wahyukusumo/RP2040-Macropad/Kicad/RP2040-Macropad/RP2040-Macropad.kicad_sch

## KiCad design Kicad/RP2040-Macropad/RP2040-Macropad.kicad_sch (2025-09-22)

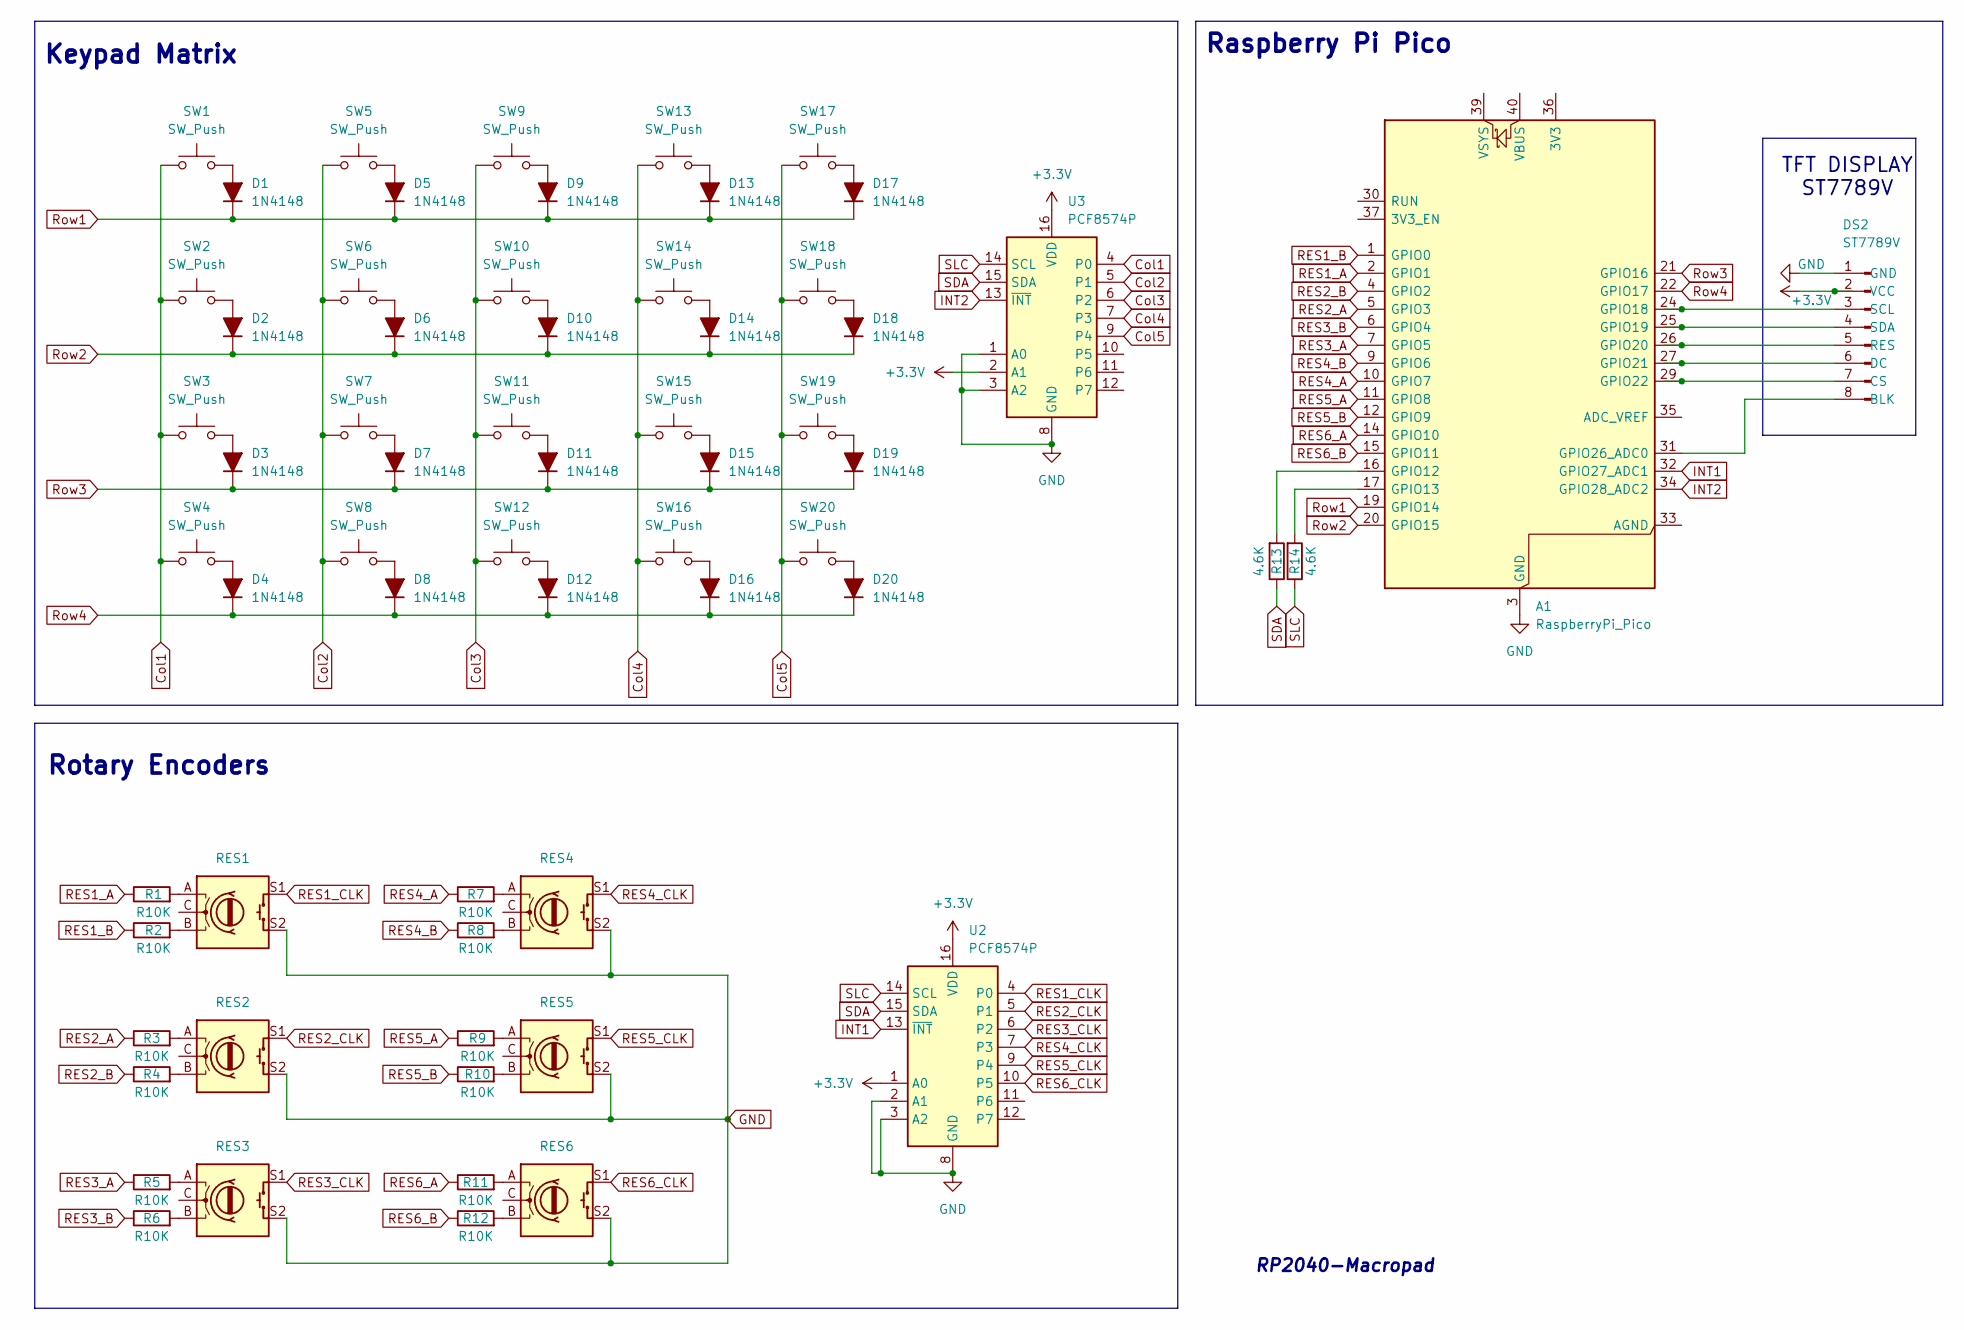
[picture p6: schematic RP2040-Macropad.kicad_sch]

Parts:
A1: RaspberryPi_Pico; RaspberryPi_Pico_Common_Unspecified
D1, D2, D3, D4, D5, D6, D7, D8, D9, D10, D11, D12, D13, D14, D15, D16, D17, D18, D19, D20: 1N4148; D_DO-35_SOD27_P7.62mm_Horizontal
DS2: ST7789V; PinHeader_1x07_P2.54mm_Vertical
R1, R2, R3, R4, R5, R6, R7, R8, R9, R10, R11, R12: R10K; R_0805_2012Metric_Pad1.20x1.40mm_HandSolder
R13, R14: 4.6K; R_Axial_DIN0204_L3.6mm_D1.6mm_P7.62mm_Horizontal
RES1_CLK1: RES1; RotaryEncoder_Alps_EC11E-Switch_Vertical_H20mm
RES2_CLK1: RES2; RotaryEncoder_Alps_EC11E-Switch_Vertical_H20mm
RES3_CLK1: RES3; RotaryEncoder_Alps_EC11E-Switch_Vertical_H20mm
RES4_CLK1: RES4; RotaryEncoder_Alps_EC11E-Switch_Vertical_H20mm
RES5_CLK1: RES5; RotaryEncoder_Alps_EC11E-Switch_Vertical_H20mm
RES6_CLK1: RES6; RotaryEncoder_Alps_EC11E-Switch_Vertical_H20mm
SW1, SW2, SW3, SW4, SW5, SW6, SW7, SW8, SW9, SW10, SW11, SW12, SW13, SW14, SW15, SW16, SW17, SW18, SW19, SW20: SW_Push; SW_Hotswap_Kailh_MX
U2, U3: PCF8574P; DIP-16_W7.62mm

Connections:
+3.3V: DS2.2 (VCC), U2.1 (A0), U2.16 (VDD), U3.2 (A1), U3.16 (VDD)
Col1: SW1.1, SW2.1, SW3.1, SW4.1, U3.4 (P0)
Col2: SW5.1, SW6.1, SW7.1, SW8.1, U3.5 (P1)
Col3: SW9.1, SW10.1, SW11.1, SW12.1, U3.6 (P2)
Col4: SW13.1, SW14.1, SW15.1, SW16.1, U3.7 (P3)
Col5: SW17.1, SW18.1, SW19.1, SW20.1, U3.9 (P4)
GND: A1.3 (GND), A1.8 (GND), A1.13 (GND), A1.18 (GND), A1.23 (GND), A1.28 (GND), A1.38 (GND), DS2.1 (GND), RES1_CLK1.S2, RES2_CLK1.S2, RES3_CLK1.S2, RES4_CLK1.S2, RES5_CLK1.S2, RES6_CLK1.S2, U2.2 (A1), U2.3 (A2), U2.8 (GND), U3.1 (A0), U3.3 (A2), U3.8 (GND)
INT1: A1.32 (GPIO27_ADC1), U2.13 (~INT)
INT2: A1.34 (GPIO28_ADC2), U3.13 (~INT)
unnamed: A1.16 (GPIO12), R13.2
unnamed: A1.17 (GPIO13), R14.2
unnamed: A1.24 (GPIO18), DS2.3 (SCL)
unnamed: A1.25 (GPIO19), DS2.4 (SDA)
unnamed: A1.26 (GPIO20), DS2.5 (RES)
unnamed: A1.27 (GPIO21), DS2.6 (DC)
unnamed: A1.29 (GPIO22), DS2.7 (CS)
unnamed: A1.31 (GPIO26_ADC0), DS2.8 (BLK)
unnamed: D1.2 (A), SW1.2
unnamed: D2.2 (A), SW2.2
unnamed: D3.2 (A), SW3.2
unnamed: D4.2 (A), SW4.2
unnamed: D5.2 (A), SW5.2
unnamed: D6.2 (A), SW6.2
unnamed: D7.2 (A), SW7.2
unnamed: D8.2 (A), SW8.2
unnamed: D9.2 (A), SW9.2
unnamed: D10.2 (A), SW10.2
unnamed: D11.2 (A), SW11.2
unnamed: D12.2 (A), SW12.2
unnamed: D13.2 (A), SW13.2
unnamed: D14.2 (A), SW14.2
unnamed: D15.2 (A), SW15.2
unnamed: D16.2 (A), SW16.2
unnamed: D17.2 (A), SW17.2
unnamed: D18.2 (A), SW18.2
unnamed: D19.2 (A), SW19.2
unnamed: D20.2 (A), SW20.2
unnamed: R1.2, RES1_CLK1.A
unnamed: R2.2, RES1_CLK1.B
unnamed: R3.2, RES2_CLK1.A
unnamed: R4.2, RES2_CLK1.B
unnamed: R5.2, RES3_CLK1.A
unnamed: R6.2, RES3_CLK1.B
unnamed: R7.2, RES4_CLK1.A
unnamed: R8.2, RES4_CLK1.B
unnamed: R9.2, RES5_CLK1.A
unnamed: R10.2, RES5_CLK1.B
unnamed: R11.2, RES6_CLK1.A
unnamed: R12.2, RES6_CLK1.B
RES1_A: A1.2 (GPIO1), R1.1
RES1_B: A1.1 (GPIO0), R2.1
RES1_CLK: RES1_CLK1.S1, U2.4 (P0)
RES2_A: A1.5 (GPIO3), R3.1
RES2_B: A1.4 (GPIO2), R4.1
RES2_CLK: RES2_CLK1.S1, U2.5 (P1)
RES3_A: A1.7 (GPIO5), R5.1
RES3_B: A1.6 (GPIO4), R6.1
RES3_CLK: RES3_CLK1.S1, U2.6 (P2)
RES4_A: A1.10 (GPIO7), R7.1
RES4_B: A1.9 (GPIO6), R8.1
RES4_CLK: RES4_CLK1.S1, U2.7 (P3)
RES5_A: A1.11 (GPIO8), R9.1
RES5_B: A1.12 (GPIO9), R10.1
RES5_CLK: RES5_CLK1.S1, U2.9 (P4)
RES6_A: A1.14 (GPIO10), R11.1
RES6_B: A1.15 (GPIO11), R12.1
RES6_CLK: RES6_CLK1.S1, U2.10 (P5)
Row1: A1.19 (GPIO14), D1.1 (K), D5.1 (K), D9.1 (K), D13.1 (K), D17.1 (K)
Row2: A1.20 (GPIO15), D2.1 (K), D6.1 (K), D10.1 (K), D14.1 (K), D18.1 (K)
Row3: A1.21 (GPIO16), D3.1 (K), D7.1 (K), D11.1 (K), D15.1 (K), D19.1 (K)
Row4: A1.22 (GPIO17), D4.1 (K), D8.1 (K), D12.1 (K), D16.1 (K), D20.1 (K)
SDA: R13.1, U2.15 (SDA), U3.15 (SDA)
SLC: R14.1, U2.14 (SCL), U3.14 (SCL)

Notes on the sheet:
Raspberry Pi Pico
Rotary Encoders
RP2040-Macropad
TFT DISPLAY ST7789V
Keypad Matrix
